Stephanehk/Hephaestus_Hand/Images/FullSizeRender (1).jpg

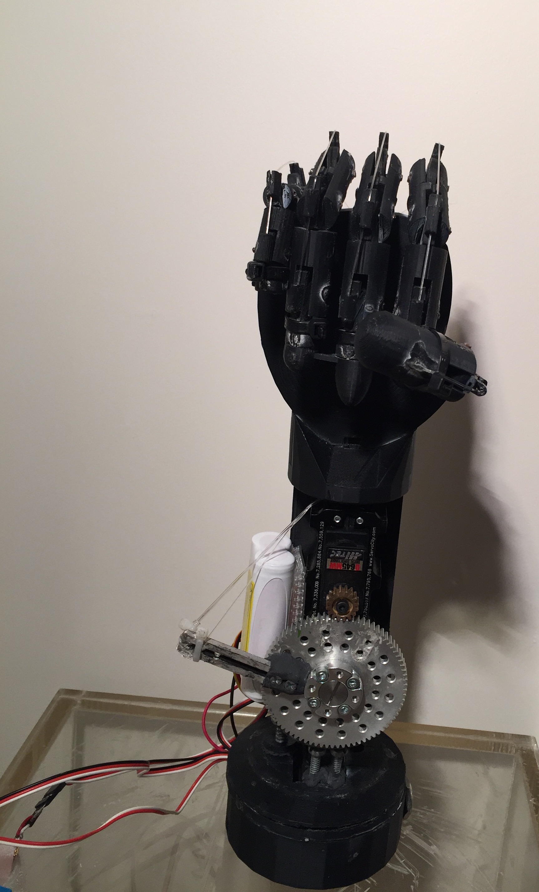
Images/FullSizeRender (1).jpg
