Stephanehk/Hephaestus_Hand/Images/HHI1.3.png

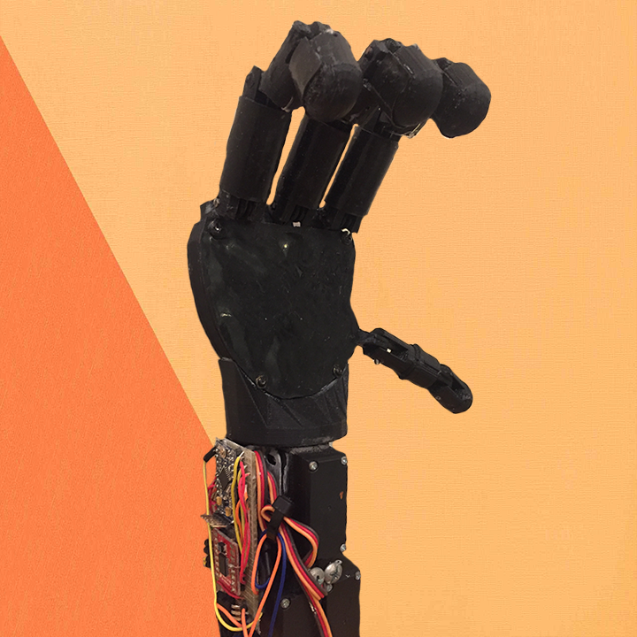
Images/HHI1.3.png
