Stephanehk/Hephaestus_Hand/Images/IMG_9781.JPG

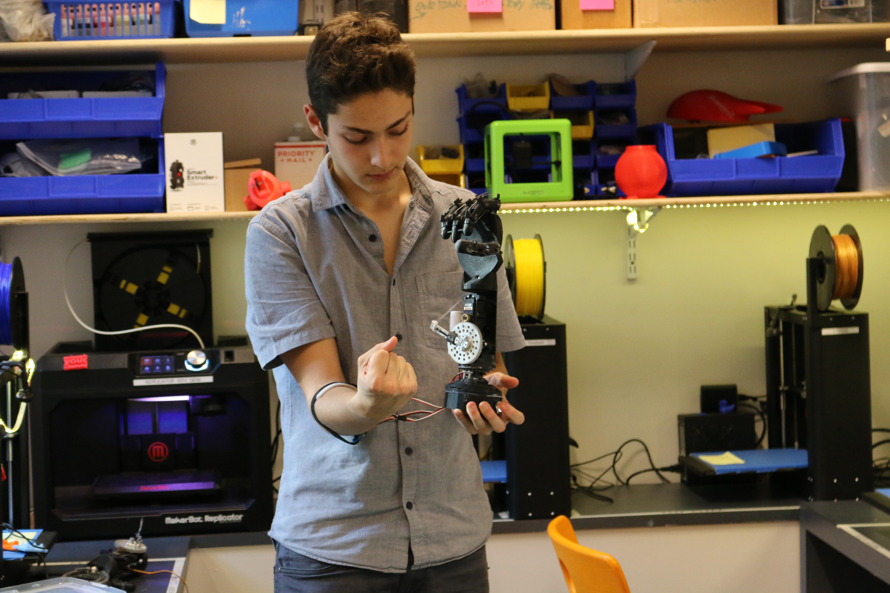
Images/IMG_9781.JPG
