Stephanehk/Hephaestus_Hand/Images/IMG_9867 (1).JPG

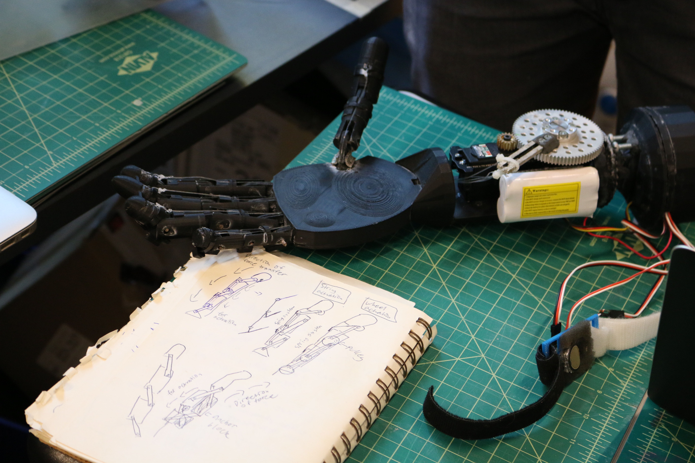
Images/IMG_9867 (1).JPG
