Stephanehk/Hephaestus_Hand/Images/Screen Shot 2017-11-04 at 4.23.33 PM.png

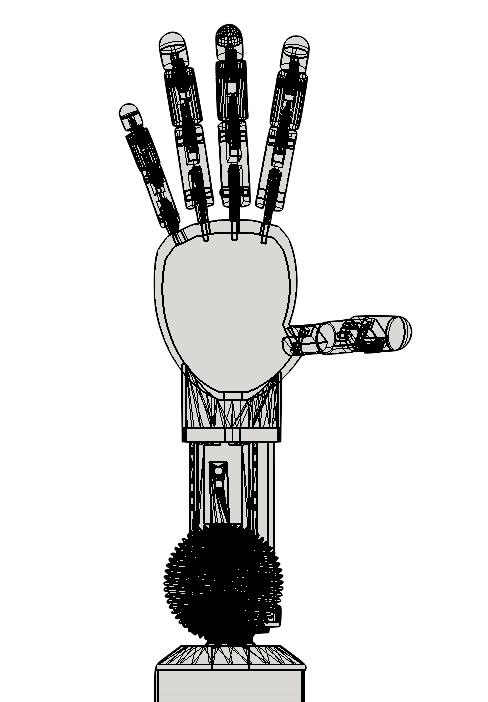
Images/Screen Shot 2017-11-04 at 4.23.33 PM.png
