Stephanehk/Hephaestus_Hand/Images/Screen Shot 2018-01-17 at 6.31.33 PM.png

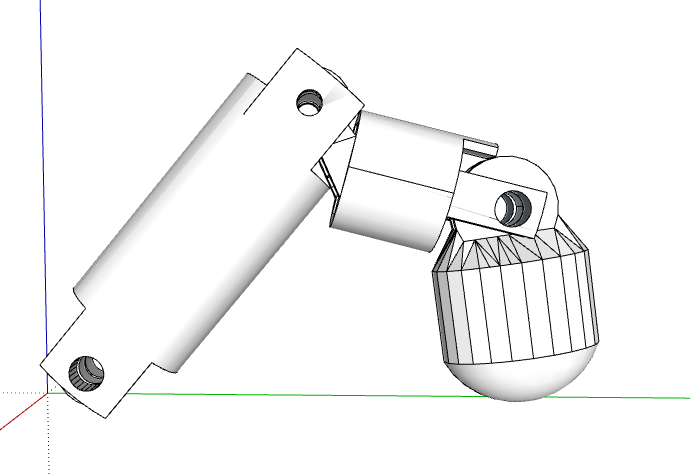
Images/Screen Shot 2018-01-17 at 6.31.33 PM.png
