Stephanehk/Hephaestus_Hand/Images/Screen Shot 2018-03-01 at 3.19.52 PM.png

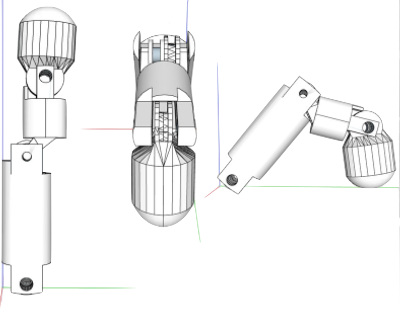
Images/Screen Shot 2018-03-01 at 3.19.52 PM.png
