Stephanehk/Hephaestus_Hand/Images/Screen Shot 2018-08-30 at 10.25.18 AM.png

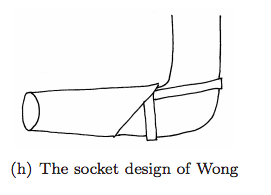
Images/Screen Shot 2018-08-30 at 10.25.18 AM.png
