Stephanehk/Hephaestus_Hand/Images/IMG_9849.JPG

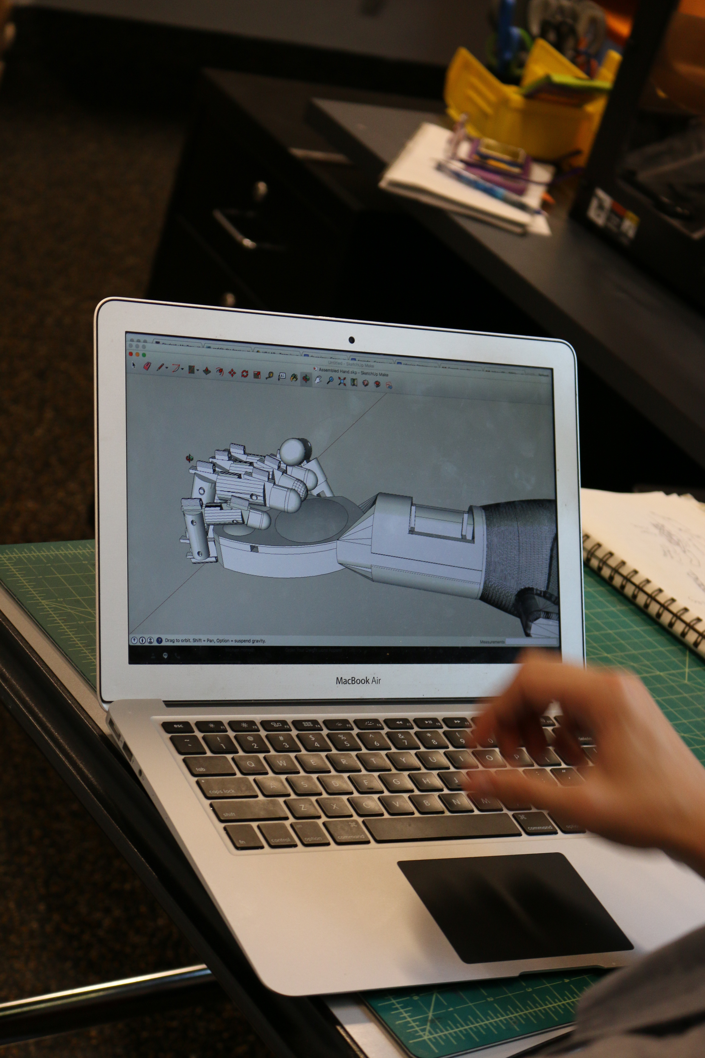
Images/IMG_9849.JPG
